TheThingsProducts/gateway/firmware/src/system_config/TTN_Gateway_v1/system_init.c

/*******************************************************************************
  System Initialization File

  File Name:
    system_init.c

  Summary:
    This file contains source code necessary to initialize the system.

  Description:
    This file contains source code necessary to initialize the system.  It
    implements the "SYS_Initialize" function, defines the configuration bits, 
    and allocates any necessary global system resources, such as the 
    sysObj structure that contains the object handles to all the MPLAB Harmony 
    module objects in the system.
 *******************************************************************************/

// DOM-IGNORE-BEGIN
/*******************************************************************************
Copyright (c) 2013-2015 released Microchip Technology Inc.  All rights reserved.

Microchip licenses to you the right to use, modify, copy and distribute
Software only when embedded on a Microchip microcontroller or digital signal
controller that is integrated into your product or third party product
(pursuant to the sublicense terms in the accompanying license agreement).

You should refer to the license agreement accompanying this Software for
additional information regarding your rights and obligations.

SOFTWARE AND DOCUMENTATION ARE PROVIDED AS IS WITHOUT WARRANTY OF ANY KIND,
EITHER EXPRESS OR IMPLIED, INCLUDING WITHOUT LIMITATION, ANY WARRANTY OF
MERCHANTABILITY, TITLE, NON-INFRINGEMENT AND FITNESS FOR A PARTICULAR PURPOSE.
IN NO EVENT SHALL MICROCHIP OR ITS LICENSORS BE LIABLE OR OBLIGATED UNDER
CONTRACT, NEGLIGENCE, STRICT LIABILITY, CONTRIBUTION, BREACH OF WARRANTY, OR
OTHER LEGAL EQUITABLE THEORY ANY DIRECT OR INDIRECT DAMAGES OR EXPENSES
INCLUDING BUT NOT LIMITED TO ANY INCIDENTAL, SPECIAL, INDIRECT, PUNITIVE OR
CONSEQUENTIAL DAMAGES, LOST PROFITS OR LOST DATA, COST OF PROCUREMENT OF
SUBSTITUTE GOODS, TECHNOLOGY, SERVICES, OR ANY CLAIMS BY THIRD PARTIES
(INCLUDING BUT NOT LIMITED TO ANY DEFENSE THEREOF), OR OTHER SIMILAR COSTS.
 *******************************************************************************/
// DOM-IGNORE-END

// *****************************************************************************
// *****************************************************************************
// Section: Included Files
// *****************************************************************************
// *****************************************************************************

#include "system_config.h"
#include "system_definitions.h"
#include "version.h"
#include "bootloader_version.h"
#include "error_messages.h"


// ****************************************************************************
// ****************************************************************************
// Section: Configuration Bits
// ****************************************************************************
// ****************************************************************************
// <editor-fold defaultstate="collapsed" desc="Configuration Bits">

/*** DEVCFG0 ***/

#pragma config DEBUG =      OFF
#pragma config JTAGEN =     ON
#pragma config ICESEL =     ICS_PGx2
#pragma config TRCEN =      OFF
#pragma config BOOTISA =    MIPS32
#pragma config FECCCON =    OFF_UNLOCKED
#pragma config FSLEEP =     OFF
#pragma config DBGPER =     ALLOW_PG2
#pragma config SMCLR =      MCLR_NORM
#pragma config SOSCGAIN =   GAIN_2X
#pragma config SOSCBOOST =  ON
#pragma config POSCGAIN =   GAIN_2X
#pragma config POSCBOOST =  ON
#pragma config EJTAGBEN =   NORMAL
#pragma config CP =         OFF

/*** DEVCFG1 ***/

#pragma config FNOSC =      SPLL
#pragma config DMTINTV =    WIN_127_128
#pragma config FSOSCEN =    OFF
#pragma config IESO =       OFF
#pragma config POSCMOD =    EC
#pragma config OSCIOFNC =   OFF
#pragma config FCKSM =      CSECME
#pragma config WDTPS =      PS8192
#pragma config WDTSPGM =    STOP
#pragma config FWDTEN =     OFF
#pragma config WINDIS =     NORMAL
#pragma config FWDTWINSZ =  WINSZ_25
#pragma config DMTCNT =     DMT9
#pragma config FDMTEN =     OFF
/*** DEVCFG2 ***/

#pragma config FPLLIDIV =   DIV_3
#pragma config FPLLRNG =    RANGE_8_16_MHZ
#pragma config FPLLICLK =   PLL_POSC
#pragma config FPLLMULT =   MUL_50
#pragma config FPLLODIV =   DIV_2
#pragma config UPLLFSEL =   FREQ_24MHZ
/*** DEVCFG3 ***/

#pragma config USERID =     0xffff
#pragma config FMIIEN =     ON
#pragma config FETHIO =     ON
#pragma config PGL1WAY =    ON
#pragma config PMDL1WAY =   ON
#pragma config IOL1WAY =    ON
#pragma config FUSBIDIO =   OFF

/*** BF1SEQ0 ***/

#pragma config TSEQ =       0xffff
#pragma config CSEQ =       0xffff
// </editor-fold>

// *****************************************************************************
// *****************************************************************************
// Section: Driver Initialization Data
// *****************************************************************************
// *****************************************************************************
// <editor-fold defaultstate="collapsed" desc="DRV_NVM Initialization Data">
/*** FLASH Driver Initialization Data ***/
extern const uint8_t NVM_MEDIA_DATA[];
SYS_FS_MEDIA_REGION_GEOMETRY NVMGeometryTable[3] = 
{
    {
        .blockSize = 1,
        .numBlocks = (DRV_NVM_MEDIA_SIZE * 1024),
    },
    {
       .blockSize = DRV_NVM_ROW_SIZE,
       .numBlocks = ((DRV_NVM_MEDIA_SIZE * 1024)/DRV_NVM_ROW_SIZE)
    },
    {
       .blockSize = DRV_NVM_PAGE_SIZE,
       .numBlocks = ((DRV_NVM_MEDIA_SIZE * 1024)/DRV_NVM_PAGE_SIZE)
    }
};

const SYS_FS_MEDIA_GEOMETRY NVMGeometry = 
{
    .mediaProperty = SYS_FS_MEDIA_WRITE_IS_BLOCKING,
    .numReadRegions = 1,
    .numWriteRegions = 1,
    .numEraseRegions = 1,
    .geometryTable = (SYS_FS_MEDIA_REGION_GEOMETRY *)&NVMGeometryTable
};

const DRV_NVM_INIT drvNvmInit =
{
    .moduleInit.sys.powerState = SYS_MODULE_POWER_RUN_FULL,
    .nvmID = NVM_ID_0,
    .interruptSource = INT_SOURCE_FLASH_CONTROL,

    .mediaStartAddress = 0x9D010000,
    .nvmMediaGeometry = (SYS_FS_MEDIA_GEOMETRY *)&NVMGeometry

};


// </editor-fold>
// <editor-fold defaultstate="collapsed" desc="DRV_SDCARD Initialization Data">
/*** SDCARD Driver Initialization Data ***/

const DRV_SDCARD_INIT drvSDCardInit =
{
    .spiId = SPI_ID_2,
    .spiIndex = 0,
    .sdcardSpeedHz = 20000000,
    .spiClk = CLK_BUS_PERIPHERAL_2,
    .chipSelectPort = PORT_CHANNEL_C,
    .chipSelectBitPosition = PORTS_BIT_POS_2,
};
// </editor-fold>
// <editor-fold defaultstate="collapsed" desc="DRV_SPI Initialization Data"> 
 /*** SPI Driver Initialization Data ***/
  /*** Index 0  ***/
 DRV_SPI_INIT drvSpi0InitData =
 {
    .spiId = DRV_SPI_SPI_ID_IDX0,
    .taskMode = DRV_SPI_TASK_MODE_IDX0,
    .spiMode = DRV_SPI_SPI_MODE_IDX0,
    .allowIdleRun = DRV_SPI_ALLOW_IDLE_RUN_IDX0,
    .spiProtocolType = DRV_SPI_SPI_PROTOCOL_TYPE_IDX0,
    .commWidth = DRV_SPI_COMM_WIDTH_IDX0,
    .spiClk = DRV_SPI_SPI_CLOCK_IDX0,
    .baudRate = DRV_SPI_BAUD_RATE_IDX0,
    .bufferType = DRV_SPI_BUFFER_TYPE_IDX0,
    .clockMode = DRV_SPI_CLOCK_MODE_IDX0,
    .inputSamplePhase = DRV_SPI_INPUT_PHASE_IDX0,
    .txInterruptSource = DRV_SPI_TX_INT_SOURCE_IDX0,
    .rxInterruptSource = DRV_SPI_RX_INT_SOURCE_IDX0,
    .errInterruptSource = DRV_SPI_ERROR_INT_SOURCE_IDX0,
    .queueSize = DRV_SPI_QUEUE_SIZE_IDX0,
    .jobQueueReserveSize = DRV_SPI_RESERVED_JOB_IDX0,
 };
  /*** Index 1  ***/
 DRV_SPI_INIT drvSpi1InitData =
 {
    .spiId = DRV_SPI_SPI_ID_IDX1,
    .taskMode = DRV_SPI_TASK_MODE_IDX1,
    .spiMode = DRV_SPI_SPI_MODE_IDX1,
    .allowIdleRun = DRV_SPI_ALLOW_IDLE_RUN_IDX1,
    .spiProtocolType = DRV_SPI_SPI_PROTOCOL_TYPE_IDX1,
    .commWidth = DRV_SPI_COMM_WIDTH_IDX1,
    .spiClk = DRV_SPI_SPI_CLOCK_IDX1,
    .baudRate = DRV_SPI_BAUD_RATE_IDX1,
    .bufferType = DRV_SPI_BUFFER_TYPE_IDX1,
    .clockMode = DRV_SPI_CLOCK_MODE_IDX1,
    .inputSamplePhase = DRV_SPI_INPUT_PHASE_IDX1,
    .txInterruptSource = DRV_SPI_TX_INT_SOURCE_IDX1,
    .rxInterruptSource = DRV_SPI_RX_INT_SOURCE_IDX1,
    .errInterruptSource = DRV_SPI_ERROR_INT_SOURCE_IDX1,
    .txDmaChannel =         DRV_SPI_TX_DMA_CHANNEL_IDX1,
    .txDmaThreshold =       DRV_SPI_TX_DMA_THRESHOLD_IDX1,
    .rxDmaChannel =         DRV_SPI_RX_DMA_CHANNEL_IDX1,
    .rxDmaThreshold =       DRV_SPI_RX_DMA_THRESHOLD_IDX1,
    .queueSize = DRV_SPI_QUEUE_SIZE_IDX1,
    .jobQueueReserveSize = DRV_SPI_RESERVED_JOB_IDX1,
 };
  /*** Index 2  ***/
 DRV_SPI_INIT drvSpi2InitData =
 {
    .spiId = DRV_SPI_SPI_ID_IDX2,
    .taskMode = DRV_SPI_TASK_MODE_IDX2,
    .spiMode = DRV_SPI_SPI_MODE_IDX2,
    .allowIdleRun = DRV_SPI_ALLOW_IDLE_RUN_IDX2,
    .spiProtocolType = DRV_SPI_SPI_PROTOCOL_TYPE_IDX2,
    .commWidth = DRV_SPI_COMM_WIDTH_IDX2,
    .spiClk = DRV_SPI_SPI_CLOCK_IDX2,
    .baudRate = DRV_SPI_BAUD_RATE_IDX2,
    .bufferType = DRV_SPI_BUFFER_TYPE_IDX2,
    .clockMode = DRV_SPI_CLOCK_MODE_IDX2,
    .inputSamplePhase = DRV_SPI_INPUT_PHASE_IDX2,
    .txInterruptSource = DRV_SPI_TX_INT_SOURCE_IDX2,
    .rxInterruptSource = DRV_SPI_RX_INT_SOURCE_IDX2,
    .errInterruptSource = DRV_SPI_ERROR_INT_SOURCE_IDX2,
    .queueSize = DRV_SPI_QUEUE_SIZE_IDX2,
    .jobQueueReserveSize = DRV_SPI_RESERVED_JOB_IDX2,
 };
// </editor-fold>
// <editor-fold defaultstate="collapsed" desc="DRV_SST25VF064C Initialization Data">
// *****************************************************************************
/* SST25VF064C Driver Initialization Data
*/

const DRV_SST25VF064C_INIT drvSst25vf064c0InitData =
{
    .moduleInit = {DRV_SST25VF064C_POWER_STATE_IDX0},
    .spiDriverModuleIndex = DRV_SST25VF064C_SPI_DRIVER_INSTANCE_IDX0, 
    .holdPortChannel = DRV_SST25VF064C_HOLD_PIN_PORT_CHANNEL_IDX0,
    .holdBitPosition = DRV_SST25VF064C_HOLD_PIN_PORT_BIT_POS_IDX0,
    .writeProtectPortChannel = DRV_SST25VF064C_WRITE_PROTECT_PIN_PORT_CHANNEL_IDX0,
    .writeProtectBitPosition = DRV_SST25VF064C_WRITE_PROTECT_PIN_BIT_POS_IDX0,
    .chipSelectPortChannel = DRV_SST25VF064C_CHIP_SELECT_PORT_CHANNEL_IDX0,
    .chipSelectBitPosition = DRV_SST25VF064C_CHIP_SELECT_PORT_BIT_POS_IDX0,
    .queueSize = DRV_SST25VF064C_QUEUE_SIZE_IDX0,
};


// </editor-fold>
// <editor-fold defaultstate="collapsed" desc="DRV_Timer Initialization Data">
/*** TMR Driver Initialization Data ***/

const DRV_TMR_INIT drvTmr0InitData =
{
    .moduleInit.sys.powerState = DRV_TMR_POWER_STATE_IDX0,
    .tmrId = DRV_TMR_PERIPHERAL_ID_IDX0,
    .clockSource = DRV_TMR_CLOCK_SOURCE_IDX0, 
    .prescale = DRV_TMR_PRESCALE_IDX0,
    .mode = DRV_TMR_OPERATION_MODE_IDX0,
    .interruptSource = DRV_TMR_INTERRUPT_SOURCE_IDX0,
    .asyncWriteEnable = false,
};
const DRV_TMR_INIT drvTmr1InitData =
{
    .moduleInit.sys.powerState = DRV_TMR_POWER_STATE_IDX1,
    .tmrId = DRV_TMR_PERIPHERAL_ID_IDX1,
    .clockSource = DRV_TMR_CLOCK_SOURCE_IDX1, 
    .prescale = DRV_TMR_PRESCALE_IDX1,
    .mode = DRV_TMR_OPERATION_MODE_16_BIT,
    .interruptSource = DRV_TMR_INTERRUPT_SOURCE_IDX1,
    .asyncWriteEnable = false,
};
// </editor-fold>
// <editor-fold defaultstate="collapsed" desc="DRV_USART Initialization Data">

const DRV_USART_INIT drvUsart0InitData =
{
    .moduleInit.value = DRV_USART_POWER_STATE_IDX0,
    .usartID = DRV_USART_PERIPHERAL_ID_IDX0, 
    .mode = DRV_USART_OPER_MODE_IDX0,
    .flags = DRV_USART_INIT_FLAGS_IDX0,
    .brgClock = DRV_USART_BRG_CLOCK_IDX0,
    .lineControl = DRV_USART_LINE_CNTRL_IDX0,
    .baud = DRV_USART_BAUD_RATE_IDX0,
    .handshake = DRV_USART_HANDSHAKE_MODE_IDX0,
    .interruptTransmit = DRV_USART_XMIT_INT_SRC_IDX0,
    .interruptReceive = DRV_USART_RCV_INT_SRC_IDX0,
    .interruptError = DRV_USART_ERR_INT_SRC_IDX0,
    .queueSizeTransmit = DRV_USART_XMIT_QUEUE_SIZE_IDX0,
    .queueSizeReceive = DRV_USART_RCV_QUEUE_SIZE_IDX0,
    .dmaChannelTransmit = DMA_CHANNEL_NONE,
    .dmaInterruptTransmit = DRV_USART_XMIT_INT_SRC_IDX0,    
    .dmaChannelReceive = DMA_CHANNEL_NONE,
    .dmaInterruptReceive = DRV_USART_RCV_INT_SRC_IDX0,    
};

const DRV_USART_INIT drvUsart1InitData =
{
    .moduleInit.value = DRV_USART_POWER_STATE_IDX1,
    .usartID = DRV_USART_PERIPHERAL_ID_IDX1, 
    .mode = DRV_USART_OPER_MODE_IDX1,
    .flags = DRV_USART_INIT_FLAGS_IDX1,
    .brgClock = DRV_USART_BRG_CLOCK_IDX1,
    .lineControl = DRV_USART_LINE_CNTRL_IDX1,
    .baud = DRV_USART_BAUD_RATE_IDX1,
    .handshake = DRV_USART_HANDSHAKE_MODE_IDX1,
    .interruptTransmit = DRV_USART_XMIT_INT_SRC_IDX1,
    .interruptReceive = DRV_USART_RCV_INT_SRC_IDX1,
    .interruptError = DRV_USART_ERR_INT_SRC_IDX1,
    .queueSizeTransmit = DRV_USART_XMIT_QUEUE_SIZE_IDX1,
    .queueSizeReceive = DRV_USART_RCV_QUEUE_SIZE_IDX1,
    .dmaChannelTransmit = DMA_CHANNEL_NONE,
    .dmaInterruptTransmit = DRV_USART_XMIT_INT_SRC_IDX1,
    .dmaChannelReceive = DMA_CHANNEL_NONE,
    .dmaInterruptReceive= DRV_USART_RCV_INT_SRC_IDX1,
};

const DRV_USART_INIT drvUsart2InitData =
{
    .moduleInit.value = DRV_USART_POWER_STATE_IDX2,
    .usartID = DRV_USART_PERIPHERAL_ID_IDX2, 
    .mode = DRV_USART_OPER_MODE_IDX2,
    .flags = DRV_USART_INIT_FLAGS_IDX2,
    .brgClock = DRV_USART_BRG_CLOCK_IDX2,
    .lineControl = DRV_USART_LINE_CNTRL_IDX2,
    .baud = DRV_USART_BAUD_RATE_IDX2,
    .handshake = DRV_USART_HANDSHAKE_MODE_IDX2,
    .interruptTransmit = DRV_USART_XMIT_INT_SRC_IDX2,
    .interruptReceive = DRV_USART_RCV_INT_SRC_IDX2,
    .interruptError = DRV_USART_ERR_INT_SRC_IDX2,
    .queueSizeTransmit = DRV_USART_XMIT_QUEUE_SIZE_IDX2,
    .queueSizeReceive = DRV_USART_RCV_QUEUE_SIZE_IDX2,
    .dmaChannelTransmit = DMA_CHANNEL_NONE,
    .dmaInterruptTransmit = DRV_USART_XMIT_INT_SRC_IDX2,
    .dmaChannelReceive = DMA_CHANNEL_NONE,
    .dmaInterruptReceive = DRV_USART_RCV_INT_SRC_IDX2,
};
// </editor-fold>

// *****************************************************************************
// *****************************************************************************
// Section: System Data
// *****************************************************************************
// *****************************************************************************

/* Structure to hold the object handles for the modules in the system. */
SYSTEM_OBJECTS sysObj;

// *****************************************************************************
// *****************************************************************************
// Section: Module Initialization Data
// *****************************************************************************
// *****************************************************************************
/* Net Presentation Layer Data Definitions */
#include "framework/net/pres/net_pres_enc_glue.h"

static const NET_PRES_TransportObject netPresTransObject0SS = {
    .fpOpen        = (NET_PRES_TransOpen)TCPIP_TCP_ServerOpen,
    .fpLocalBind         = (NET_PRES_TransBind)TCPIP_TCP_Bind,
    .fpRemoteBind        = (NET_PRES_TransBind)TCPIP_TCP_RemoteBind,
    .fpOptionGet         = (NET_PRES_TransOption)TCPIP_TCP_OptionsGet,
    .fpOptionSet         = (NET_PRES_TransOption)TCPIP_TCP_OptionsSet,
    .fpIsConnected       = (NET_PRES_TransBool)TCPIP_TCP_IsConnected,
    .fpWasReset          = (NET_PRES_TransBool)TCPIP_TCP_WasReset,
    .fpDisconnect        = (NET_PRES_TransBool)TCPIP_TCP_Disconnect,
    .fpConnect           = (NET_PRES_TransBool)TCPIP_TCP_Connect,
    .fpClose             = (NET_PRES_TransClose)TCPIP_TCP_Close,
    .fpSocketInfoGet     = (NET_PRES_TransSocketInfoGet)TCPIP_TCP_SocketInfoGet,
    .fpFlush             = (NET_PRES_TransBool)TCPIP_TCP_Flush,
    .fpPeek              = (NET_PRES_TransPeek)TCPIP_TCP_ArrayPeek,
    .fpDiscard           = (NET_PRES_TransDiscard)TCPIP_TCP_Discard,
    .fpHandlerRegister   = (NET_PRES_TransHandlerRegister)TCPIP_TCP_SignalHandlerRegister,
    .fpHandlerDeregister = (NET_PRES_TransSignalHandlerDeregister)TCPIP_TCP_SignalHandlerDeregister,
    .fpRead              = (NET_PRES_TransRead)TCPIP_TCP_ArrayGet,
    .fpWrite             = (NET_PRES_TransWrite)TCPIP_TCP_ArrayPut,
    .fpReadyToRead       = (NET_PRES_TransReady)TCPIP_TCP_GetIsReady,
    .fpReadyToWrite      = (NET_PRES_TransReady)TCPIP_TCP_PutIsReady,
    .fpIsPortDefaultSecure = (NET_PRES_TransIsPortDefaultSecured)TCPIP_Helper_TCPSecurePortGet,
};
static const NET_PRES_TransportObject netPresTransObject0SC = {
    .fpOpen        = (NET_PRES_TransOpen)TCPIP_TCP_ClientOpen,
    .fpLocalBind         = (NET_PRES_TransBind)TCPIP_TCP_Bind,
    .fpRemoteBind        = (NET_PRES_TransBind)TCPIP_TCP_RemoteBind,
    .fpOptionGet         = (NET_PRES_TransOption)TCPIP_TCP_OptionsGet,
    .fpOptionSet         = (NET_PRES_TransOption)TCPIP_TCP_OptionsSet,
    .fpIsConnected       = (NET_PRES_TransBool)TCPIP_TCP_IsConnected,
    .fpWasReset          = (NET_PRES_TransBool)TCPIP_TCP_WasReset,
    .fpDisconnect        = (NET_PRES_TransBool)TCPIP_TCP_Disconnect,
    .fpConnect           = (NET_PRES_TransBool)TCPIP_TCP_Connect,
    .fpClose             = (NET_PRES_TransClose)TCPIP_TCP_Close,
    .fpSocketInfoGet     = (NET_PRES_TransSocketInfoGet)TCPIP_TCP_SocketInfoGet,
    .fpFlush             = (NET_PRES_TransBool)TCPIP_TCP_Flush,
    .fpPeek              = (NET_PRES_TransPeek)TCPIP_TCP_ArrayPeek,
    .fpDiscard           = (NET_PRES_TransDiscard)TCPIP_TCP_Discard,
    .fpHandlerRegister   = (NET_PRES_TransHandlerRegister)TCPIP_TCP_SignalHandlerRegister,
    .fpHandlerDeregister = (NET_PRES_TransSignalHandlerDeregister)TCPIP_TCP_SignalHandlerDeregister,
    .fpRead              = (NET_PRES_TransRead)TCPIP_TCP_ArrayGet,
    .fpWrite             = (NET_PRES_TransWrite)TCPIP_TCP_ArrayPut,
    .fpReadyToRead       = (NET_PRES_TransReady)TCPIP_TCP_GetIsReady,
    .fpReadyToWrite      = (NET_PRES_TransReady)TCPIP_TCP_PutIsReady,
    .fpIsPortDefaultSecure = (NET_PRES_TransIsPortDefaultSecured)TCPIP_Helper_TCPSecurePortGet,
};
static const NET_PRES_TransportObject netPresTransObject0DS = {
    .fpOpen        = (NET_PRES_TransOpen)TCPIP_UDP_ServerOpen,
    .fpLocalBind         = (NET_PRES_TransBind)TCPIP_UDP_Bind,
    .fpRemoteBind        = (NET_PRES_TransBind)TCPIP_UDP_RemoteBind,
    .fpOptionGet         = (NET_PRES_TransOption)TCPIP_UDP_OptionsGet,
    .fpOptionSet         = (NET_PRES_TransOption)TCPIP_UDP_OptionsSet,
    .fpIsConnected       = (NET_PRES_TransBool)TCPIP_UDP_IsConnected,
    .fpWasReset          = NULL,
    .fpDisconnect        = (NET_PRES_TransBool)TCPIP_UDP_Disconnect,
    .fpConnect          = NULL,
    .fpClose             = (NET_PRES_TransClose)TCPIP_UDP_Close,
    .fpSocketInfoGet     = (NET_PRES_TransSocketInfoGet)TCPIP_UDP_SocketInfoGet,
    .fpFlush             = (NET_PRES_TransBool)TCPIP_UDP_Flush,
    .fpPeek              = NULL,
    .fpDiscard           = (NET_PRES_TransDiscard)TCPIP_UDP_Discard,
    .fpHandlerRegister   = (NET_PRES_TransHandlerRegister)TCPIP_UDP_SignalHandlerRegister,
    .fpHandlerDeregister = (NET_PRES_TransSignalHandlerDeregister)TCPIP_UDP_SignalHandlerDeregister,
    .fpRead              = (NET_PRES_TransRead)TCPIP_UDP_ArrayGet,
    .fpWrite             = (NET_PRES_TransWrite)TCPIP_UDP_ArrayPut,
    .fpReadyToRead       = (NET_PRES_TransReady)TCPIP_UDP_GetIsReady,
    .fpReadyToWrite      = (NET_PRES_TransReady)TCPIP_UDP_PutIsReady,
    .fpIsPortDefaultSecure = (NET_PRES_TransIsPortDefaultSecured)TCPIP_Helper_UDPSecurePortGet,
};
static const NET_PRES_TransportObject netPresTransObject0DC = {
    .fpOpen        = (NET_PRES_TransOpen)TCPIP_UDP_ClientOpen,
    .fpLocalBind         = (NET_PRES_TransBind)TCPIP_UDP_Bind,
    .fpRemoteBind        = (NET_PRES_TransBind)TCPIP_UDP_RemoteBind,
    .fpOptionGet         = (NET_PRES_TransOption)TCPIP_UDP_OptionsGet,
    .fpOptionSet         = (NET_PRES_TransOption)TCPIP_UDP_OptionsSet,
    .fpIsConnected       = (NET_PRES_TransBool)TCPIP_UDP_IsConnected,
    .fpWasReset          = NULL,
    .fpDisconnect        = (NET_PRES_TransBool)TCPIP_UDP_Disconnect,
    .fpConnect          = NULL,
    .fpClose             = (NET_PRES_TransClose)TCPIP_UDP_Close,
    .fpSocketInfoGet     = (NET_PRES_TransSocketInfoGet)TCPIP_UDP_SocketInfoGet,
    .fpFlush             = (NET_PRES_TransBool)TCPIP_UDP_Flush,
    .fpPeek              = NULL,
    .fpDiscard           = (NET_PRES_TransDiscard)TCPIP_UDP_Discard,
    .fpHandlerRegister   = (NET_PRES_TransHandlerRegister)TCPIP_UDP_SignalHandlerRegister,
    .fpHandlerDeregister = (NET_PRES_TransSignalHandlerDeregister)TCPIP_UDP_SignalHandlerDeregister,
    .fpRead              = (NET_PRES_TransRead)TCPIP_UDP_ArrayGet,
    .fpWrite             = (NET_PRES_TransWrite)TCPIP_UDP_ArrayPut,
    .fpReadyToRead       = (NET_PRES_TransReady)TCPIP_UDP_GetIsReady,
    .fpReadyToWrite      = (NET_PRES_TransReady)TCPIP_UDP_PutIsReady,
    .fpIsPortDefaultSecure = (NET_PRES_TransIsPortDefaultSecured)TCPIP_Helper_UDPSecurePortGet,
};
static const NET_PRES_INST_DATA netPresCfgs[] = 
{
    {
        .pTransObject_ss = &netPresTransObject0SS,
        .pTransObject_sc = &netPresTransObject0SC,
        .pTransObject_ds = &netPresTransObject0DS,
        .pTransObject_dc = &netPresTransObject0DC,
        .pProvObject_ss = NULL,
        .pProvObject_sc = &net_pres_EncProviderStreamClient0,
        .pProvObject_ds = NULL,
        .pProvObject_dc = NULL,
    },
};

static const NET_PRES_INIT_DATA netPresInitData = 
{
    .numLayers = sizeof(netPresCfgs) / sizeof(NET_PRES_INST_DATA),
    .pInitData = netPresCfgs
};
  
 
// <editor-fold defaultstate="collapsed" desc="SYS_COMMAND Initialization Data">
/*** System Command Initialization Data ***/

SYS_CMD_INIT sysCmdInit =
{
    .moduleInit = {0},
    .consoleCmdIOParam = SYS_CMD_SINGLE_CHARACTER_READ_CONSOLE_IO_PARAM,
};
// </editor-fold>
// <editor-fold defaultstate="collapsed" desc="SYS_CONSOLE Initialization Data">
/*** System Console Initialization Data ***/

SYS_MODULE_OBJ sysConsoleObjects[] = { SYS_MODULE_OBJ_INVALID };

/* Declared in console device implementation (sys_console_uart.c) */
extern SYS_CONSOLE_DEV_DESC consUsartDevDesc;
SYS_CONSOLE_INIT consUsartInit0 =
{
    .moduleInit = {0},
    .consDevDesc = &consUsartDevDesc,
};
// </editor-fold>
// <editor-fold defaultstate="collapsed" desc="SYS_DEBUG Initialization Data">
/*** System Debug Initialization Data ***/

SYS_DEBUG_INIT debugInit =
{
    .moduleInit = {0},
    .errorLevel = SYS_ERROR_INFO
};
// </editor-fold>
//<editor-fold defaultstate="collapsed" desc="SYS_DEVCON Initialization Data">
/*******************************************************************************
  Device Control System Service Initialization Data
*/

const SYS_DEVCON_INIT sysDevconInit =
{
    .moduleInit = {0},
};

// </editor-fold>
//<editor-fold defaultstate="collapsed" desc="SYS_DMA Initialization Data">
/*** System DMA Initialization Data ***/

const SYS_DMA_INIT sysDmaInit =
{
	.sidl = SYS_DMA_SIDL_DISABLE,

};
// </editor-fold>
// <editor-fold defaultstate="collapsed" desc="SYS_FS Initialization Data">
/*** File System Initialization Data ***/

const SYS_FS_MEDIA_MOUNT_DATA sysfsMountTable[SYS_FS_VOLUME_NUMBER] = 
{
	{NULL}
};


const SYS_FS_REGISTRATION_TABLE sysFSInit [ SYS_FS_MAX_FILE_SYSTEM_TYPE ] =
{
    {
        .nativeFileSystemType = FAT,
        .nativeFileSystemFunctions = &FatFsFunctions
    },
    {
        .nativeFileSystemType = MPFS2,
        .nativeFileSystemFunctions = &MPFSFunctions
    }

};



// </editor-fold>
// <editor-fold defaultstate="collapsed" desc="SYS_TMR Initialization Data">
/*** TMR Service Initialization Data ***/
const SYS_TMR_INIT sysTmrInitData =
{
    .moduleInit = {SYS_MODULE_POWER_RUN_FULL},
    .drvIndex = DRV_TMR_INDEX_0,
    .tmrFreq = 1000, 
};
// </editor-fold>

// *****************************************************************************
// *****************************************************************************
// Section: Library/Stack Initialization Data
// *****************************************************************************
// *****************************************************************************
// <editor-fold defaultstate="collapsed" desc="TCPIP Stack Initialization Data">
// *****************************************************************************
// *****************************************************************************
// Section: TCPIP Data
// *****************************************************************************
// *****************************************************************************

/*** ARP Service Initialization Data ***/
const TCPIP_ARP_MODULE_CONFIG tcpipARPInitData =
{ 
    .cacheEntries       = TCPIP_ARP_CACHE_ENTRIES,     
    .deleteOld          = TCPIP_ARP_CACHE_DELETE_OLD,    
    .entrySolvedTmo     = TCPIP_ARP_CACHE_SOLVED_ENTRY_TMO, 
    .entryPendingTmo    = TCPIP_ARP_CACHE_PENDING_ENTRY_TMO, 
    .entryRetryTmo      = TCPIP_ARP_CACHE_PENDING_RETRY_TMO, 
    .permQuota          = TCPIP_ARP_CACHE_PERMANENT_QUOTA, 
    .purgeThres         = TCPIP_ARP_CACHE_PURGE_THRESHOLD, 
    .purgeQuanta        = TCPIP_ARP_CACHE_PURGE_QUANTA, 
    .retries            = TCPIP_ARP_CACHE_ENTRY_RETRIES, 
    .gratProbeCount     = TCPIP_ARP_GRATUITOUS_PROBE_COUNT,
};



/*** UDP Sockets Initialization Data ***/
const TCPIP_UDP_MODULE_CONFIG tcpipUDPInitData =
{
    .nSockets       = TCPIP_UDP_MAX_SOCKETS,
    .sktTxBuffSize  = TCPIP_UDP_SOCKET_DEFAULT_TX_SIZE, 
};

/*** TCP Sockets Initialization Data ***/
const TCPIP_TCP_MODULE_CONFIG tcpipTCPInitData =
{
    .nSockets       = TCPIP_TCP_MAX_SOCKETS,
    .sktTxBuffSize  = TCPIP_TCP_SOCKET_DEFAULT_TX_SIZE, 
    .sktRxBuffSize  = TCPIP_TCP_SOCKET_DEFAULT_RX_SIZE,
};

/*** HTTP Server Initialization Data ***/
const TCPIP_HTTP_MODULE_CONFIG tcpipHTTPInitData =
{
    .nConnections   = TCPIP_HTTP_MAX_CONNECTIONS,
    .nTlsConnections    = TCPIP_HTTP_MAX_TLS_CONNECTIONS,
    .dataLen		= TCPIP_HTTP_MAX_DATA_LEN,
    .sktTxBuffSize	= TCPIP_HTTP_SKT_TX_BUFF_SIZE,
    .sktRxBuffSize	= TCPIP_HTTP_SKT_RX_BUFF_SIZE,
    .tlsSktTxBuffSize	= TCPIP_HTTP_TLS_SKT_TX_BUFF_SIZE,
    .tlsSktRxBuffSize	= TCPIP_HTTP_TLS_SKT_RX_BUFF_SIZE,
    .configFlags	= TCPIP_HTTP_CONFIG_FLAGS,
};


/*** SNTP Client Initialization Data ***/
const TCPIP_SNTP_MODULE_CONFIG tcpipSNTPInitData =
{
    .ntp_server		        = TCPIP_NTP_SERVER,
    .ntp_interface		    = TCPIP_NTP_DEFAULT_IF,
    .ntp_connection_type	= TCPIP_NTP_DEFAULT_CONNECTION_TYPE,
    .ntp_reply_timeout		= TCPIP_NTP_REPLY_TIMEOUT,
    .ntp_stamp_timeout		= TCPIP_NTP_TIME_STAMP_TMO,
    .ntp_success_interval	= TCPIP_NTP_QUERY_INTERVAL,
    .ntp_error_interval		= TCPIP_NTP_FAST_QUERY_INTERVAL,
};


/*** DHCP client Initialization Data ***/
const TCPIP_DHCP_MODULE_CONFIG tcpipDHCPInitData =
{     
    .dhcpEnable     = TCPIP_DHCP_CLIENT_ENABLED,   
    .dhcpTmo        = TCPIP_DHCP_TIMEOUT,
    .dhcpCliPort    = TCPIP_DHCP_CLIENT_CONNECT_PORT,
    .dhcpSrvPort    = TCPIP_DHCP_SERVER_LISTEN_PORT,

};


/*** ICMP Server Initialization Data ***/
const TCPIP_ICMP_MODULE_CONFIG tcpipICMPInitData = 
{
};

/*** NBNS Server Initialization Data ***/
const TCPIP_NBNS_MODULE_CONFIG tcpipNBNSInitData =
{ 
};

/*** ETH MAC Initialization Data ***/
const TCPIP_MODULE_MAC_PIC32INT_CONFIG tcpipMACPIC32INTInitData =
{ 
    .nTxDescriptors         = TCPIP_EMAC_TX_DESCRIPTORS,
    .rxBuffSize             = TCPIP_EMAC_RX_BUFF_SIZE,
    .nRxDescriptors         = TCPIP_EMAC_RX_DESCRIPTORS,
    .nRxDedicatedBuffers    = TCPIP_EMAC_RX_DEDICATED_BUFFERS,
    .nRxInitBuffers         = TCPIP_EMAC_RX_INIT_BUFFERS,
    .rxLowThreshold         = TCPIP_EMAC_RX_LOW_THRESHOLD,
    .rxLowFill              = TCPIP_EMAC_RX_LOW_FILL,
    .ethFlags               = TCPIP_EMAC_ETH_OPEN_FLAGS,
    .phyFlags               = TCPIP_EMAC_PHY_CONFIG_FLAGS,
    .linkInitDelay          = TCPIP_EMAC_PHY_LINK_INIT_DELAY,
    .phyAddress             = TCPIP_EMAC_PHY_ADDRESS,
    .ethModuleId            = TCPIP_EMAC_MODULE_ID,
    .pPhyObject             = &DRV_ETHPHY_OBJECT_MICREL_KSZ8061RND,
    .pPhyBase               = &DRV_ETHPHY_OBJECT_BASE_Default,
};

/*** Wi-Fi Interface MRF24WN Initialization Data ***/
const TCPIP_MODULE_MAC_MRF24WN_CONFIG macMRF24WNConfigData ={
};


/*** Zeroconfig initialization data ***/
const ZCLL_MODULE_CONFIG tcpipZCLLInitData =
{
};


/*** DHCP server initialization data ***/
TCPIP_DHCPS_ADDRESS_CONFIG DHCP_POOL_CONFIG[]=
{
    {
        .interfaceIndex     = TCPIP_DHCP_SERVER_INTERFACE_INDEX_IDX0,
        .serverIPAddress    = TCPIP_DHCPS_DEFAULT_SERVER_IP_ADDRESS_IDX0,
        .startIPAddRange    = TCPIP_DHCPS_DEFAULT_IP_ADDRESS_RANGE_START_IDX0,
        .ipMaskAddress      = TCPIP_DHCPS_DEFAULT_SERVER_NETMASK_ADDRESS_IDX0,
        .priDNS             = TCPIP_DHCPS_DEFAULT_SERVER_PRIMARY_DNS_ADDRESS_IDX0,
        .secondDNS          = TCPIP_DHCPS_DEFAULT_SERVER_SECONDARY_DNS_ADDRESS_IDX0,
        .poolEnabled        = TCPIP_DHCP_SERVER_POOL_ENABLED_IDX0,
    },
};
const TCPIP_DHCPS_MODULE_CONFIG tcpipDHCPSInitData =
{
    .enabled            = true,
    .deleteOldLease     = TCPIP_DHCP_SERVER_DELETE_OLD_ENTRIES,
    .leaseEntries       = TCPIP_DHCPS_LEASE_ENTRIES_DEFAULT,
    .entrySolvedTmo     = TCPIP_DHCPS_LEASE_SOLVED_ENTRY_TMO,
    .dhcpServer         = (TCPIP_DHCPS_ADDRESS_CONFIG*)DHCP_POOL_CONFIG,
};


/*** DNS Client Initialization Data ***/
const TCPIP_DNS_CLIENT_MODULE_CONFIG tcpipDNSClientInitData =
{
    .deleteOldLease         = TCPIP_DNS_CLIENT_DELETE_OLD_ENTRIES,
    .cacheEntries           = TCPIP_DNS_CLIENT_CACHE_ENTRIES,
    .entrySolvedTmo         = TCPIP_DNS_CLIENT_CACHE_ENTRY_TMO,    
    .nIPv4Entries  = TCPIP_DNS_CLIENT_CACHE_PER_IPV4_ADDRESS,
    .ipAddressType       = TCPIP_DNS_CLIENT_ADDRESS_TYPE,
    .nIPv6Entries  = TCPIP_DNS_CLIENT_CACHE_PER_IPV6_ADDRESS,
};




TCPIP_STACK_HEAP_EXTERNAL_CONFIG tcpipHeapConfig =
{
    .heapType = TCPIP_STACK_HEAP_TYPE_EXTERNAL_HEAP,
    .heapFlags = TCPIP_STACK_HEAP_USE_FLAGS,
    .heapUsage = TCPIP_STACK_HEAP_USAGE_CONFIG,
    .malloc_fnc = TCPIP_STACK_MALLOC_FUNC,
    .calloc_fnc = TCPIP_STACK_CALLOC_FUNC,
    .free_fnc = TCPIP_STACK_FREE_FUNC,
};
 
const TCPIP_NETWORK_CONFIG __attribute__((unused))  TCPIP_HOSTS_CONFIGURATION[] =
{
/*** Network Configuration Index 0 ***/
    {
        TCPIP_NETWORK_DEFAULT_INTERFACE_NAME,       // interface
        TCPIP_NETWORK_DEFAULT_HOST_NAME,            // hostName
        TCPIP_NETWORK_DEFAULT_MAC_ADDR,             // macAddr
        TCPIP_NETWORK_DEFAULT_IP_ADDRESS,           // ipAddr
        TCPIP_NETWORK_DEFAULT_IP_MASK,              // ipMask
        TCPIP_NETWORK_DEFAULT_GATEWAY,              // gateway
        TCPIP_NETWORK_DEFAULT_DNS,                  // priDNS
        TCPIP_NETWORK_DEFAULT_SECOND_DNS,           // secondDNS
        TCPIP_NETWORK_DEFAULT_POWER_MODE,           // powerMode
        TCPIP_NETWORK_DEFAULT_INTERFACE_FLAGS,      // startFlags
       &TCPIP_NETWORK_DEFAULT_MAC_DRIVER,           // pMacObject
    },
/*** Network Configuration Index 1 ***/
    {
        TCPIP_NETWORK_DEFAULT_INTERFACE_NAME_IDX1,       // interface
        TCPIP_NETWORK_DEFAULT_HOST_NAME_IDX1,            // hostName
        TCPIP_NETWORK_DEFAULT_MAC_ADDR_IDX1,             // macAddr
        TCPIP_NETWORK_DEFAULT_IP_ADDRESS_IDX1,           // ipAddr
        TCPIP_NETWORK_DEFAULT_IP_MASK_IDX1,              // ipMask
        TCPIP_NETWORK_DEFAULT_GATEWAY_IDX1,              // gateway
        TCPIP_NETWORK_DEFAULT_DNS_IDX1,                  // priDNS
        TCPIP_NETWORK_DEFAULT_SECOND_DNS_IDX1,           // secondDNS
        TCPIP_NETWORK_DEFAULT_POWER_MODE_IDX1,           // powerMode
        TCPIP_NETWORK_DEFAULT_INTERFACE_FLAGS_IDX1,      // startFlags
       &TCPIP_NETWORK_DEFAULT_MAC_DRIVER_IDX1,           // pMacObject
    },
};

const TCPIP_STACK_MODULE_CONFIG TCPIP_STACK_MODULE_CONFIG_TBL [] =
{
    {TCPIP_MODULE_IPV4,          0},
    {TCPIP_MODULE_ICMP,          0},                           // TCPIP_MODULE_ICMP
    {TCPIP_MODULE_ARP,           &tcpipARPInitData},              // TCPIP_MODULE_ARP
    {TCPIP_MODULE_UDP,           &tcpipUDPInitData},              // TCPIP_MODULE_UDP,
    {TCPIP_MODULE_TCP,           &tcpipTCPInitData},              // TCPIP_MODULE_TCP,
    {TCPIP_MODULE_DHCP_CLIENT,   &tcpipDHCPInitData},             // TCPIP_MODULE_DHCP_CLIENT,
    {TCPIP_MODULE_DHCP_SERVER,   &tcpipDHCPSInitData},                           // TCPIP_MODULE_DHCP_SERVER,
    {TCPIP_MODULE_DNS_CLIENT,&tcpipDNSClientInitData}, // TCPIP_MODULE_DNS_CLIENT,
    {TCPIP_MODULE_NBNS,          &tcpipNBNSInitData},                           // TCPIP_MODULE_NBNS
    {TCPIP_MODULE_SNTP,    &tcpipSNTPInitData},                            // TCPIP_MODULE_SNTP,

    {TCPIP_MODULE_HTTP_SERVER,   &tcpipHTTPInitData},              // TCPIP_MODULE_HTTP_SERVER,
    {TCPIP_MODULE_ZCLL, 0},                                    // TCPIP_MODULE_ZCLL,
    {TCPIP_MODULE_MDNS, 0},                                    // TCPIP_MODULE_MDNS,
    { TCPIP_MODULE_MANAGER,    & tcpipHeapConfig },          // TCPIP_MODULE_MANAGER
    // MAC modules
    {TCPIP_MODULE_MAC_PIC32INT, &tcpipMACPIC32INTInitData},     // TCPIP_MODULE_MAC_PIC32INT
    {TCPIP_MODULE_MAC_MRF24WN, &macMRF24WNConfigData},        // TCPIP_MODULE_MAC_MRF24WN

};

/*********************************************************************
 * Function:        SYS_MODULE_OBJ TCPIP_STACK_Init()
 *
 * PreCondition:    None
 *
 * Input:
 *
 * Output:          valid system module object if Stack and its componets are initialized
 *                  SYS_MODULE_OBJ_INVALID otherwise
 *
 * Overview:        The function starts the initialization of the stack.
 *                  If an error occurs, the SYS_ERROR() is called
 *                  and the function de-initialize itself and will return false.
 *
 * Side Effects:    None
 *
 * Note:            This function must be called before any of the
 *                  stack or its component routines are used.
 *
 ********************************************************************/


SYS_MODULE_OBJ TCPIP_STACK_Init()
{
    TCPIP_STACK_INIT    tcpipInit;

    tcpipInit.moduleInit.sys.powerState = SYS_MODULE_POWER_RUN_FULL;
    tcpipInit.pNetConf = TCPIP_HOSTS_CONFIGURATION;
    tcpipInit.nNets = sizeof (TCPIP_HOSTS_CONFIGURATION) / sizeof (*TCPIP_HOSTS_CONFIGURATION);
    tcpipInit.pModConfig = TCPIP_STACK_MODULE_CONFIG_TBL;
    tcpipInit.nModules = sizeof (TCPIP_STACK_MODULE_CONFIG_TBL) / sizeof (*TCPIP_STACK_MODULE_CONFIG_TBL);

    return TCPIP_STACK_Initialize(0, &tcpipInit.moduleInit);
}
// </editor-fold>

// *****************************************************************************
// *****************************************************************************
// Section: Static Initialization Functions
// *****************************************************************************
// *****************************************************************************


// *****************************************************************************
// *****************************************************************************
// Section: System Initialization
// *****************************************************************************
// *****************************************************************************

/*******************************************************************************
  Function:
    void SYS_Initialize ( void *data )

  Summary:
    Initializes the board, services, drivers, application and other modules.

  Remarks:
    See prototype in system/common/sys_module.h.
 */

void SYS_Initialize ( void* data )
{
    /* Core Processor Initialization */
    SYS_CLK_Initialize( NULL );
    sysObj.sysDevcon = SYS_DEVCON_Initialize(SYS_DEVCON_INDEX_0, (SYS_MODULE_INIT*)&sysDevconInit);
    SYS_DEVCON_PerformanceConfig(SYS_CLK_SystemFrequencyGet());
    SYS_DEVCON_JTAGEnable();
    SYS_PORTS_Initialize();

    /* Initialize Drivers */

    /*** SPI Driver Index 0 initialization***/

    SYS_INT_VectorPrioritySet(DRV_SPI_TX_INT_VECTOR_IDX0, DRV_SPI_TX_INT_PRIORITY_IDX0);
    SYS_INT_VectorSubprioritySet(DRV_SPI_TX_INT_VECTOR_IDX0, DRV_SPI_TX_INT_SUB_PRIORITY_IDX0);
    SYS_INT_VectorPrioritySet(DRV_SPI_RX_INT_VECTOR_IDX0, DRV_SPI_RX_INT_PRIORITY_IDX0);
    SYS_INT_VectorSubprioritySet(DRV_SPI_RX_INT_VECTOR_IDX0, DRV_SPI_RX_INT_SUB_PRIORITY_IDX0);
    SYS_INT_VectorPrioritySet(DRV_DRV_SPI_ERROR_INT_VECTOR_IDX0, DRV_SPI_ERROR_INT_PRIORITY_IDX0);
    SYS_INT_VectorSubprioritySet(DRV_DRV_SPI_ERROR_INT_VECTOR_IDX0, DRV_SPI_ERROR_INT_SUB_PRIORITY_IDX0);
    sysObj.spiObjectIdx0 = DRV_SPI_Initialize(DRV_SPI_INDEX_0, (const SYS_MODULE_INIT  * const)&drvSpi0InitData);

    /*** SPI Driver Index 1 initialization***/

    SYS_INT_VectorPrioritySet(DRV_SPI_TX_INT_VECTOR_IDX1, DRV_SPI_TX_INT_PRIORITY_IDX1);
    SYS_INT_VectorSubprioritySet(DRV_SPI_TX_INT_VECTOR_IDX1, DRV_SPI_TX_INT_SUB_PRIORITY_IDX1);
    SYS_INT_VectorPrioritySet(DRV_SPI_RX_INT_VECTOR_IDX1, DRV_SPI_RX_INT_PRIORITY_IDX1);
    SYS_INT_VectorSubprioritySet(DRV_SPI_RX_INT_VECTOR_IDX1, DRV_SPI_RX_INT_SUB_PRIORITY_IDX1);
    SYS_INT_VectorPrioritySet(DRV_DRV_SPI_ERROR_INT_VECTOR_IDX1, DRV_SPI_ERROR_INT_PRIORITY_IDX1);
    SYS_INT_VectorSubprioritySet(DRV_DRV_SPI_ERROR_INT_VECTOR_IDX1, DRV_SPI_ERROR_INT_SUB_PRIORITY_IDX1);
    sysObj.spiObjectIdx1 = DRV_SPI_Initialize(DRV_SPI_INDEX_1, (const SYS_MODULE_INIT  * const)&drvSpi1InitData);

    /*** SPI Driver Index 2 initialization***/

    SYS_INT_VectorPrioritySet(DRV_SPI_TX_INT_VECTOR_IDX2, DRV_SPI_TX_INT_PRIORITY_IDX2);
    SYS_INT_VectorSubprioritySet(DRV_SPI_TX_INT_VECTOR_IDX2, DRV_SPI_TX_INT_SUB_PRIORITY_IDX2);
    SYS_INT_VectorPrioritySet(DRV_SPI_RX_INT_VECTOR_IDX2, DRV_SPI_RX_INT_PRIORITY_IDX2);
    SYS_INT_VectorSubprioritySet(DRV_SPI_RX_INT_VECTOR_IDX2, DRV_SPI_RX_INT_SUB_PRIORITY_IDX2);
    SYS_INT_VectorPrioritySet(DRV_DRV_SPI_ERROR_INT_VECTOR_IDX2, DRV_SPI_ERROR_INT_PRIORITY_IDX2);
    SYS_INT_VectorSubprioritySet(DRV_DRV_SPI_ERROR_INT_VECTOR_IDX2, DRV_SPI_ERROR_INT_SUB_PRIORITY_IDX2);
    sysObj.spiObjectIdx2 = DRV_SPI_Initialize(DRV_SPI_INDEX_2, (const SYS_MODULE_INIT  * const)&drvSpi2InitData);
    sysObj.sysDma = SYS_DMA_Initialize((SYS_MODULE_INIT *)&sysDmaInit);
    SYS_INT_VectorPrioritySet(INT_VECTOR_DMA0, INT_PRIORITY_LEVEL2);
    SYS_INT_VectorSubprioritySet(INT_VECTOR_DMA0, INT_SUBPRIORITY_LEVEL0);
    SYS_INT_VectorPrioritySet(INT_VECTOR_DMA1, INT_PRIORITY_LEVEL2);
    SYS_INT_VectorSubprioritySet(INT_VECTOR_DMA1, INT_SUBPRIORITY_LEVEL0);

    SYS_INT_SourceEnable(INT_SOURCE_DMA_0);
    SYS_INT_SourceEnable(INT_SOURCE_DMA_1);


    /* Configure the Flash Controller Interrupt Priority */
    SYS_INT_VectorPrioritySet(INT_VECTOR_FLASH, INT_PRIORITY_LEVEL4);

    /* Configure the Flash Controller Interrupt Sub Priority */
    SYS_INT_VectorSubprioritySet(INT_VECTOR_FLASH, INT_SUBPRIORITY_LEVEL0);

    /* Initialize the NVM Driver */
    sysObj.drvNvm = DRV_NVM_Initialize(DRV_NVM_INDEX_0, (SYS_MODULE_INIT *)&drvNvmInit);
    sysObj.drvSDCard = DRV_SDCARD_Initialize(DRV_SDCARD_INDEX_0,(SYS_MODULE_INIT *)&drvSDCardInit);
    sysObj.drvSst25vf064c0 = DRV_SST25VF064C_Initialize(DRV_SST25VF064C_INDEX_0, (SYS_MODULE_INIT *)&drvSst25vf064c0InitData);




    sysObj.drvTmr0 = DRV_TMR_Initialize(DRV_TMR_INDEX_0, (SYS_MODULE_INIT *)&drvTmr0InitData);
    sysObj.drvTmr1 = DRV_TMR_Initialize(DRV_TMR_INDEX_1, (SYS_MODULE_INIT *)&drvTmr1InitData);

    SYS_INT_VectorPrioritySet(INT_VECTOR_T2, INT_PRIORITY_LEVEL4);
    SYS_INT_VectorSubprioritySet(INT_VECTOR_T2, INT_SUBPRIORITY_LEVEL0);
    SYS_INT_VectorPrioritySet(INT_VECTOR_T3, INT_PRIORITY_LEVEL4);
    SYS_INT_VectorSubprioritySet(INT_VECTOR_T3, INT_SUBPRIORITY_LEVEL0);
 
 
     sysObj.drvUsart0 = DRV_USART_Initialize(DRV_USART_INDEX_0, (SYS_MODULE_INIT *)&drvUsart0InitData);
    sysObj.drvUsart1 = DRV_USART_Initialize(DRV_USART_INDEX_1, (SYS_MODULE_INIT *)&drvUsart1InitData);
    sysObj.drvUsart2 = DRV_USART_Initialize(DRV_USART_INDEX_2, (SYS_MODULE_INIT *)&drvUsart2InitData);
    SYS_INT_VectorPrioritySet(INT_VECTOR_UART4_TX, INT_PRIORITY_LEVEL1);
    SYS_INT_VectorSubprioritySet(INT_VECTOR_UART4_TX, INT_SUBPRIORITY_LEVEL0);
    SYS_INT_VectorPrioritySet(INT_VECTOR_UART4_RX, INT_PRIORITY_LEVEL1);
    SYS_INT_VectorSubprioritySet(INT_VECTOR_UART4_RX, INT_SUBPRIORITY_LEVEL0);
    SYS_INT_VectorPrioritySet(INT_VECTOR_UART4_FAULT, INT_PRIORITY_LEVEL1);
    SYS_INT_VectorSubprioritySet(INT_VECTOR_UART4_FAULT, INT_SUBPRIORITY_LEVEL0);
    SYS_INT_VectorPrioritySet(INT_VECTOR_UART1_TX, INT_PRIORITY_LEVEL1);
    SYS_INT_VectorSubprioritySet(INT_VECTOR_UART1_TX, INT_SUBPRIORITY_LEVEL0);
    SYS_INT_VectorPrioritySet(INT_VECTOR_UART1_RX, INT_PRIORITY_LEVEL1);
    SYS_INT_VectorSubprioritySet(INT_VECTOR_UART1_RX, INT_SUBPRIORITY_LEVEL0);
    SYS_INT_VectorPrioritySet(INT_VECTOR_UART1_FAULT, INT_PRIORITY_LEVEL1);
    SYS_INT_VectorSubprioritySet(INT_VECTOR_UART1_FAULT, INT_SUBPRIORITY_LEVEL0);
    SYS_INT_VectorPrioritySet(INT_VECTOR_UART3_TX, INT_PRIORITY_LEVEL1);
    SYS_INT_VectorSubprioritySet(INT_VECTOR_UART3_TX, INT_SUBPRIORITY_LEVEL0);
    SYS_INT_VectorPrioritySet(INT_VECTOR_UART3_RX, INT_PRIORITY_LEVEL1);
    SYS_INT_VectorSubprioritySet(INT_VECTOR_UART3_RX, INT_SUBPRIORITY_LEVEL0);
    SYS_INT_VectorPrioritySet(INT_VECTOR_UART3_FAULT, INT_PRIORITY_LEVEL1);
    SYS_INT_VectorSubprioritySet(INT_VECTOR_UART3_FAULT, INT_SUBPRIORITY_LEVEL0);


    /* Initialize System Services */

    /*** Command Service Initialization Code ***/
    SYS_CMD_Initialize((SYS_MODULE_INIT*)&sysCmdInit);
    sysObj.sysConsole0 = SYS_CONSOLE_Initialize(SYS_CONSOLE_INDEX_0, (SYS_MODULE_INIT *)&consUsartInit0);


    /*** Debug Service Initialization Code ***/
    sysObj.sysDebug = SYS_DEBUG_Initialize(SYS_DEBUG_INDEX_0, (SYS_MODULE_INIT*)&debugInit);

    /*** File System Service Initialization Code ***/
    SYS_FS_Initialize( (const void *) sysFSInit );

    /*** Interrupt Service Initialization Code ***/
    SYS_INT_Initialize();

    /*** Random Service Initialization Code ***/
    SYS_RANDOM_Initialize(0, 0);

    /*** TMR Service Initialization Code ***/
    sysObj.sysTmr  = SYS_TMR_Initialize(SYS_TMR_INDEX_0, (const SYS_MODULE_INIT  * const)&sysTmrInitData);
  
    /* Initialize Middleware */
    sysObj.netPres = NET_PRES_Initialize(0, (SYS_MODULE_INIT*)&netPresInitData);

    /* set priority for ETHERNET interrupt source */
    SYS_INT_VectorPrioritySet(INT_VECTOR_ETH, INT_PRIORITY_LEVEL5);
    
    /* set sub-priority for ETHERNET interrupt source */
    SYS_INT_VectorSubprioritySet(INT_VECTOR_ETH, INT_SUBPRIORITY_LEVEL0);
    
    /* TCPIP Stack Initialization */
    sysObj.tcpip = TCPIP_STACK_Init();
    SYS_ASSERT(sysObj.tcpip != SYS_MODULE_OBJ_INVALID, "TCPIP_STACK_Init Failed" );

    
    SYS_PRINT("\r\n\r\n\r\n**************************\r\n");
    SYS_PRINT("*   The Things Network   *\r\n");
    SYS_PRINT("*      G A T E W A Y     *\r\n");
    SYS_PRINT("**************************\r\n");
    SYS_PRINT("Firmware name: %s, type: %d, version: %d.%d.%d, commit: %08x, timestamp: %d\r\n", VERSION_NAME, VERSION_TYPE, VERSION_MAJOR, VERSION_MINOR, VERSION_PATCH, VERSION_COMMIT, VERSION_TIMESTAMP);
    const bootloader_version_t *pBootloaderVersion = BootloaderVersion_Get();
    SYS_PRINT("Bootloader revision: %d, commit: %08x, timestamp: %d\r\n", pBootloaderVersion->revision, pBootloaderVersion->commit, pBootloaderVersion->timestamp);
    SYS_PRINT("Build time: %s %s\r\n",__DATE__,__TIME__);
    SYS_PRINT("Reboot reason: 0x%02X\r\n", wdt_get_reboot_reason());
    ErrorMessage_Initialize();
    SYS_PRINT("\r\n\r\n\r\n\r\n");
    
    /* Initialize the Application */
    APP_Initialize();
    LORA_Initialize();
}

/*******************************************************************************
 End of File
*/
